ashley1888/ME-507-Term-Project/docs/gripper.png

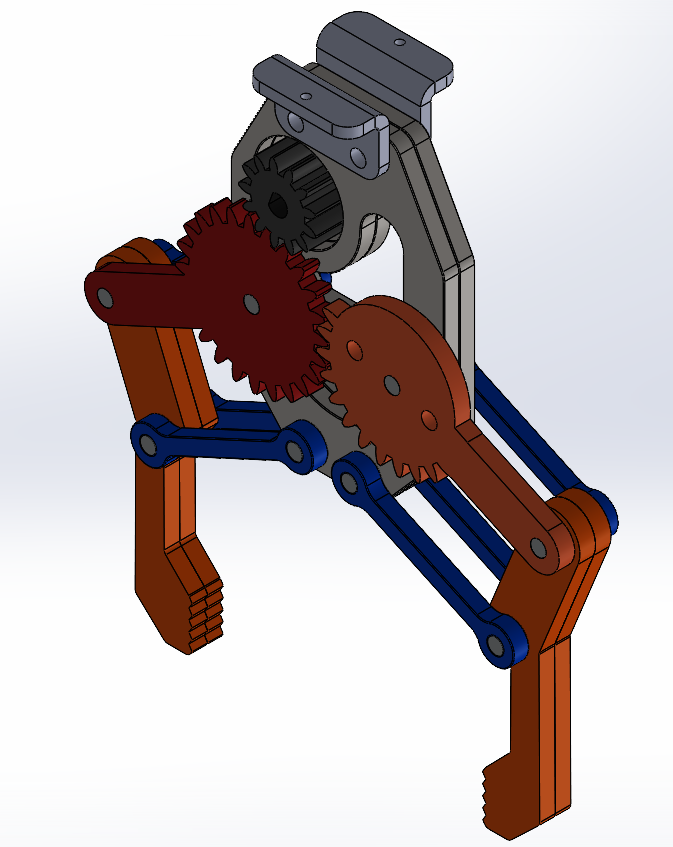
docs/gripper.png
