ashley1888/ME-507-Term-Project/docs/shaft_support_to_linear_bearing.png

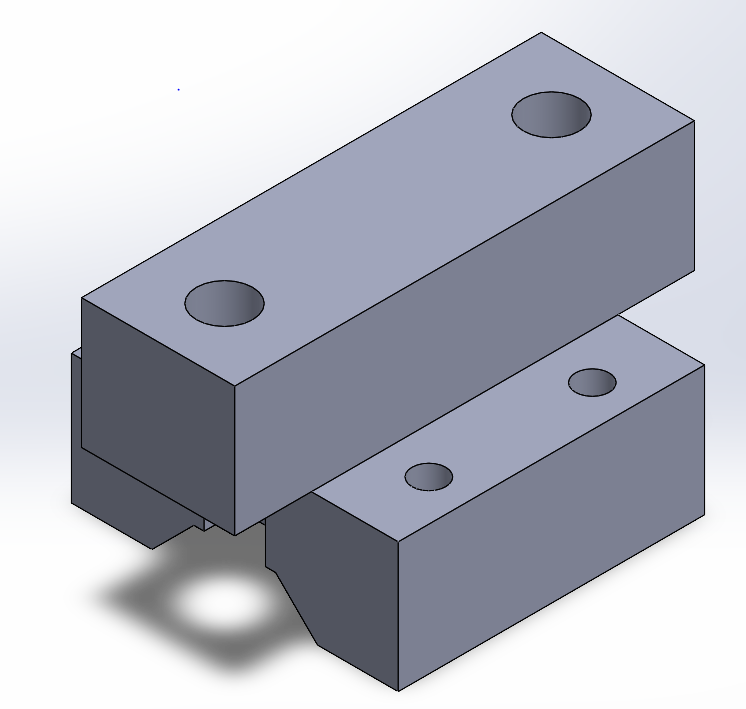
docs/shaft_support_to_linear_bearing.png
