ashley1888/ME-507-Term-Project/docs/x_motor_support.png

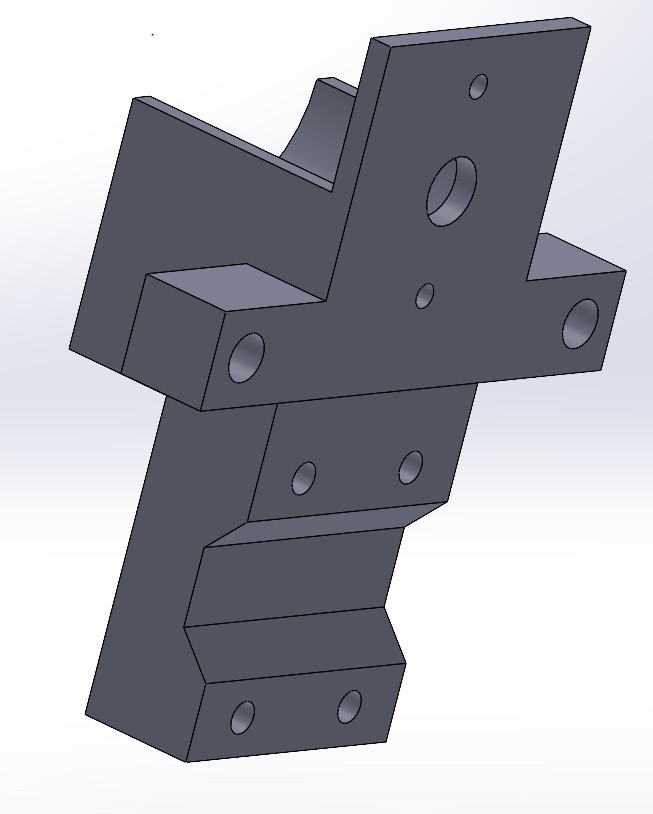
docs/x_motor_support.png
