ashley1888/ME-507-Term-Project/docs/z_motor_support.png

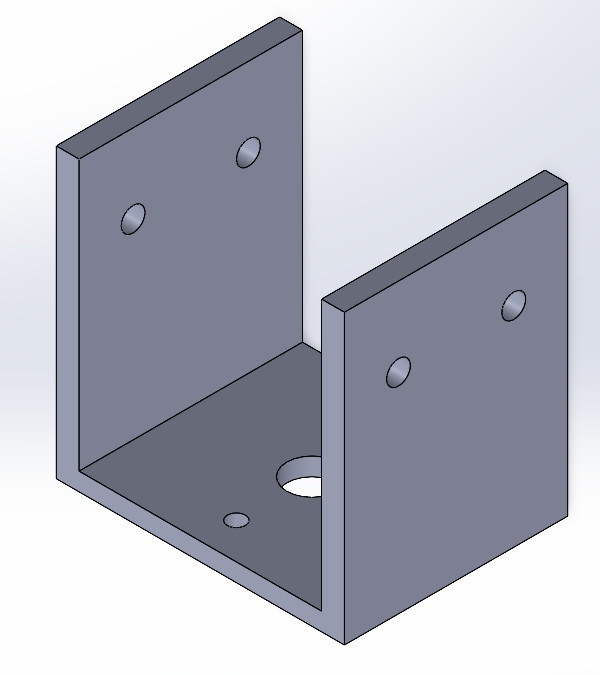
docs/z_motor_support.png
