ashley1888/ME-507-Term-Project/CAD/3D Printed Parts/Belt Clamp.SLDPRT

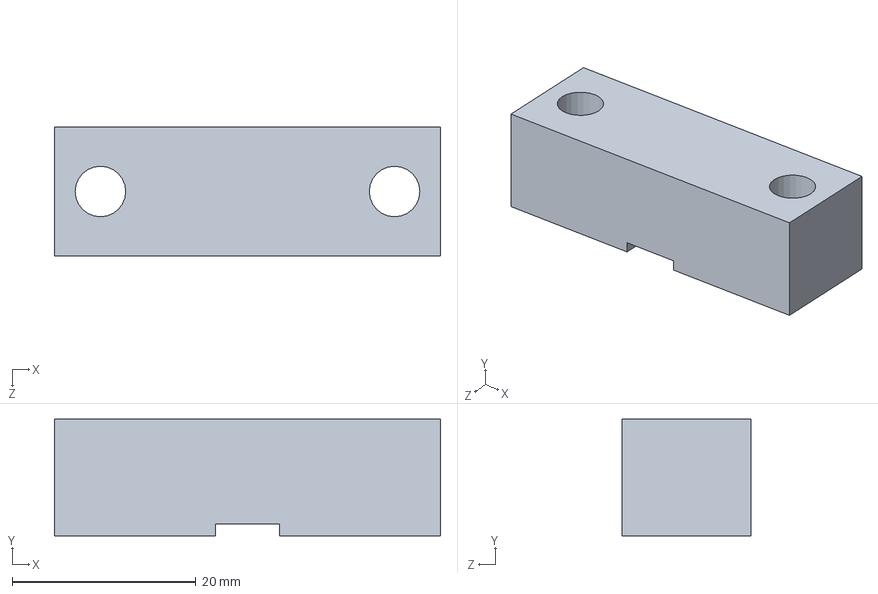
[picture p25: CAD file, 2021-12-07]
CAD/3D Printed Parts/Belt Clamp.SLDPRT
42.0 x 12.7 x 14.0 mm
