ashley1888/ME-507-Term-Project/CAD/Gripper/Part6-6.SLDPRT

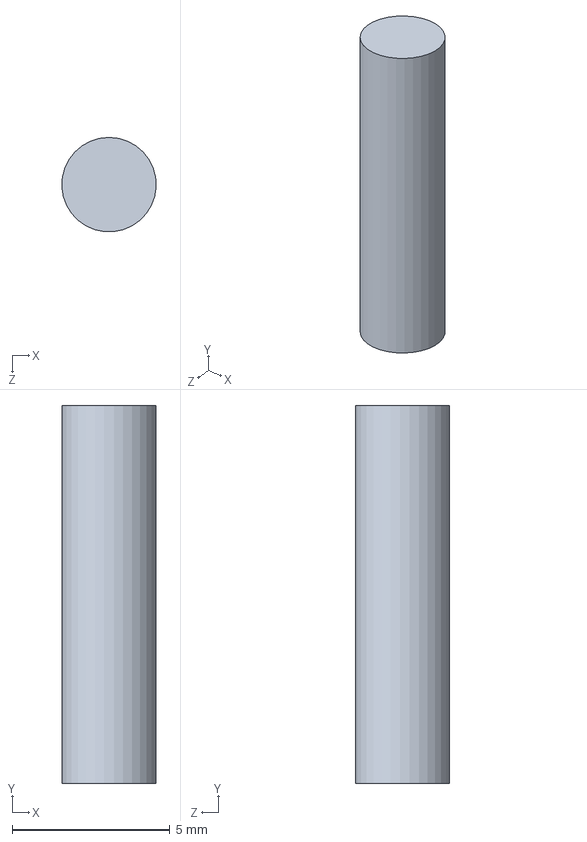
[picture p26: CAD file, 2021-12-07]
CAD/Gripper/Part6-6.SLDPRT
3.00 x 12.0 x 2.99 mm
