ashley1888/ME-507-Term-Project/CAD/Shaft Coupling.SLDPRT

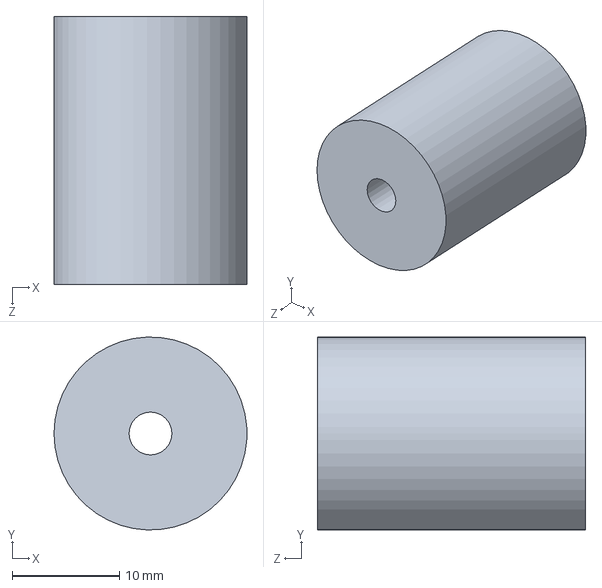
[picture p27: CAD file, 2021-12-07]
CAD/Shaft Coupling.SLDPRT
18.0 x 18.0 x 25.0 mm
