ashley1888/ME-507-Term-Project/CAD/3D Printed Parts/.stl Files/Part3-3 (x2).STL

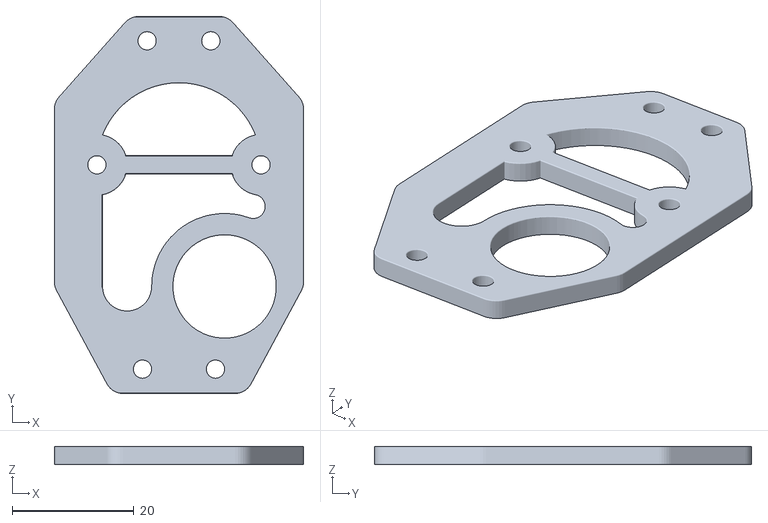
[picture p28: CAD file, 2021-12-08]
CAD/3D Printed Parts/.stl Files/Part3-3 (x2).STL
41.0 x 62.0 x 3.00
