ashley1888/ME-507-Term-Project/CAD/3D Printed Parts/Shaft Support to Linear Bearing.SLDPRT

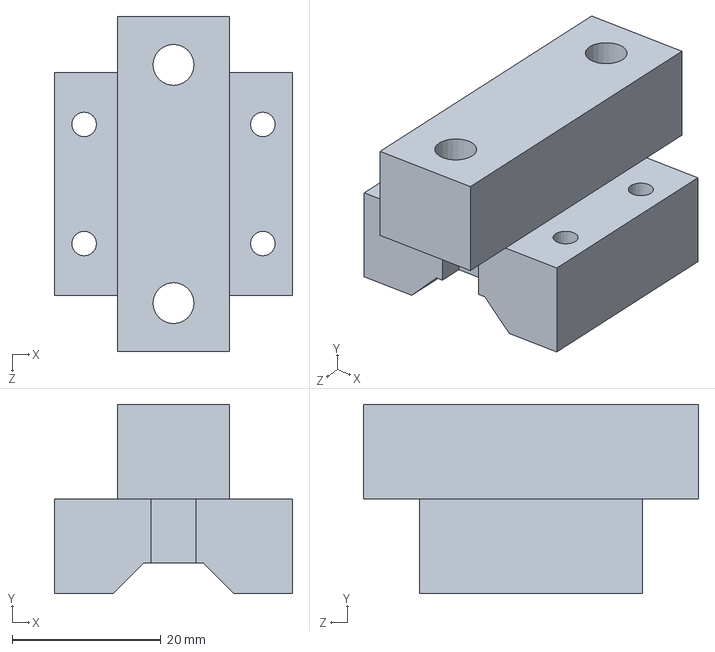
[picture p29: CAD file, 2021-12-07]
CAD/3D Printed Parts/Shaft Support to Linear Bearing.SLDPRT
32.0 x 25.4 x 45.0 mm
