ashley1888/ME-507-Term-Project/CAD/Motor.SLDPRT

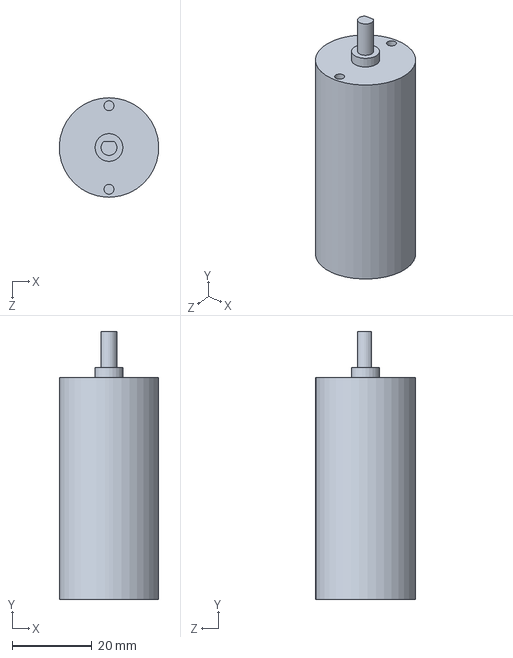
[picture p30: CAD file, 2021-12-07]
CAD/Motor.SLDPRT
25.0 x 67.3 x 25.0 mm
