ashley1888/ME-507-Term-Project/CAD/3D Printed Parts/.stl Files/Belt Holder (x2).STL

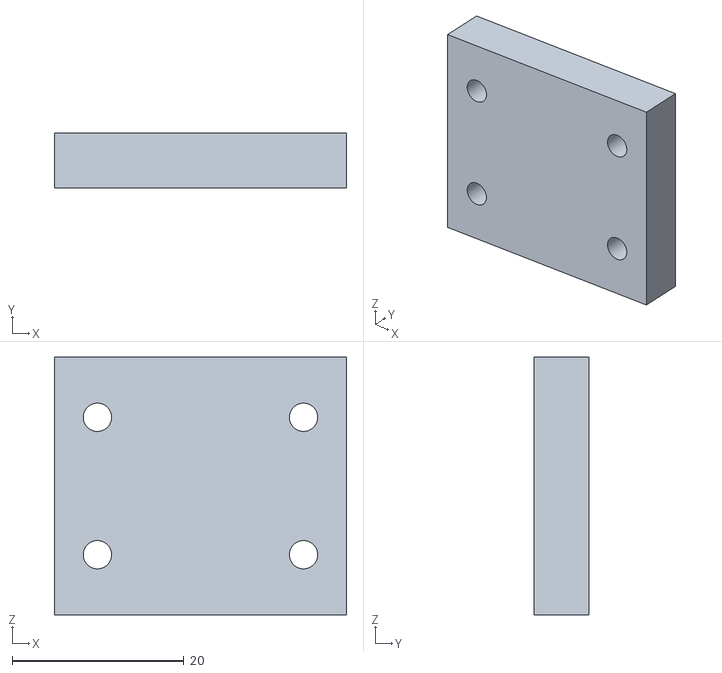
[picture p31: CAD file, 2021-12-08]
CAD/3D Printed Parts/.stl Files/Belt Holder (x2).STL
34.0 x 6.35 x 30.0
