ashley1888/ME-507-Term-Project/CAD/3D Printed Parts/Linear Rod Support Belt Holder.SLDPRT

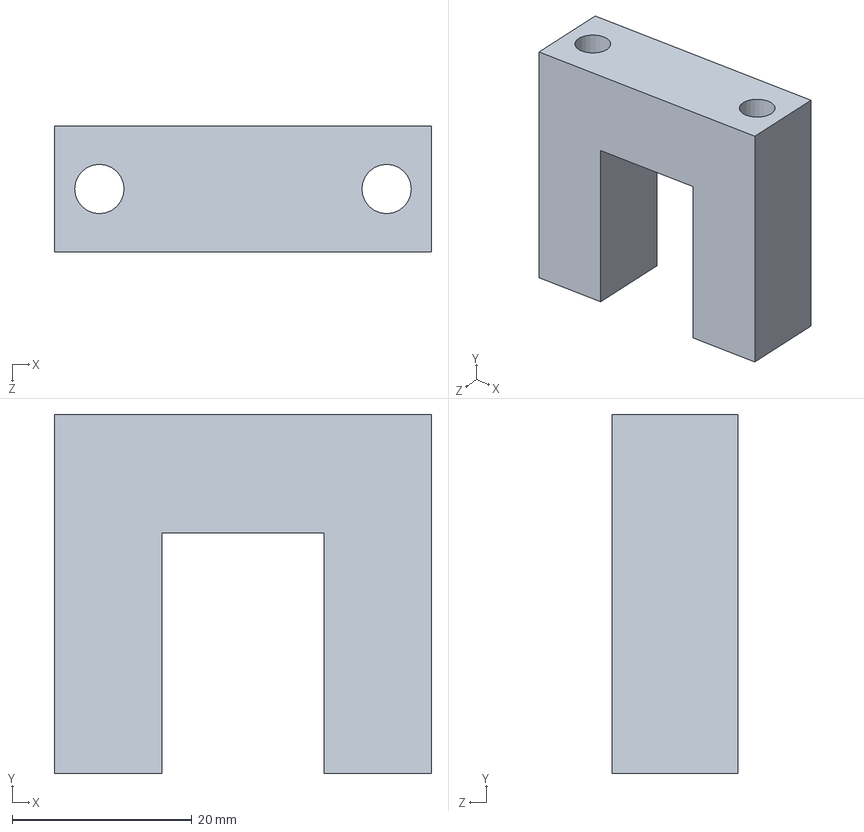
[picture p32: CAD file, 2021-12-07]
CAD/3D Printed Parts/Linear Rod Support Belt Holder.SLDPRT
42.0 x 40.0 x 14.0 mm
