ashley1888/ME-507-Term-Project/CAD/Gripper/Part7-7.SLDPRT

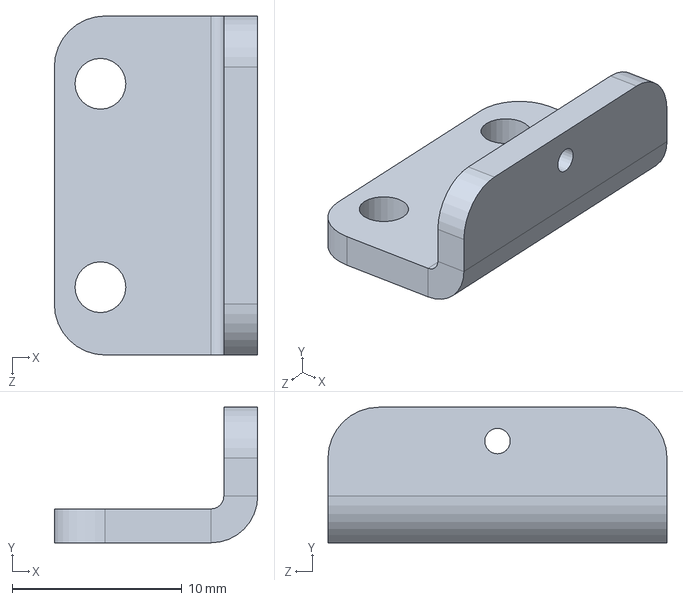
[picture p33: CAD file, 2021-12-07]
CAD/Gripper/Part7-7.SLDPRT
12.0 x 8.00 x 20.0 mm
