ashley1888/ME-507-Term-Project/CAD/Linear Ball Bearing.SLDPRT

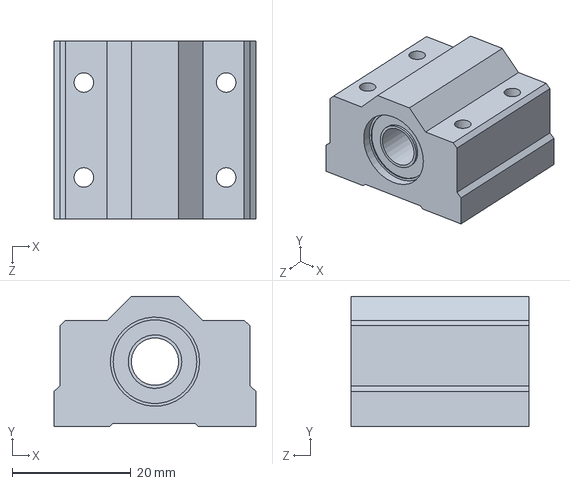
[picture p34: CAD file, 2021-12-07]
CAD/Linear Ball Bearing.SLDPRT
34.1 x 22.0 x 30.0 mm
