ashley1888/ME-507-Term-Project/CAD/3D Printed Parts/.stl Files/part4-4 (x1).STL

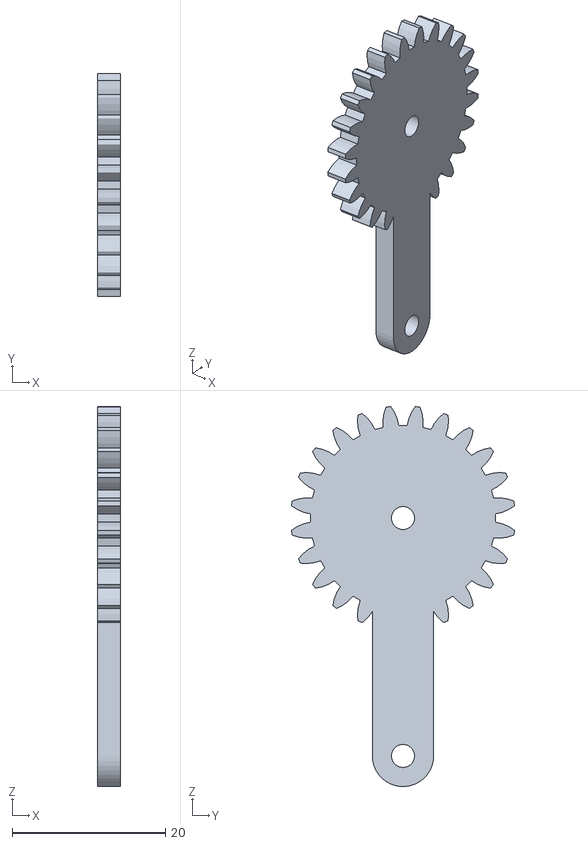
[picture p35: CAD file, 2021-12-08]
CAD/3D Printed Parts/.stl Files/part4-4 (x1).STL
3.00 x 29.1 x 49.5
