ashley1888/ME-507-Term-Project/CAD/Linear Rod.SLDPRT

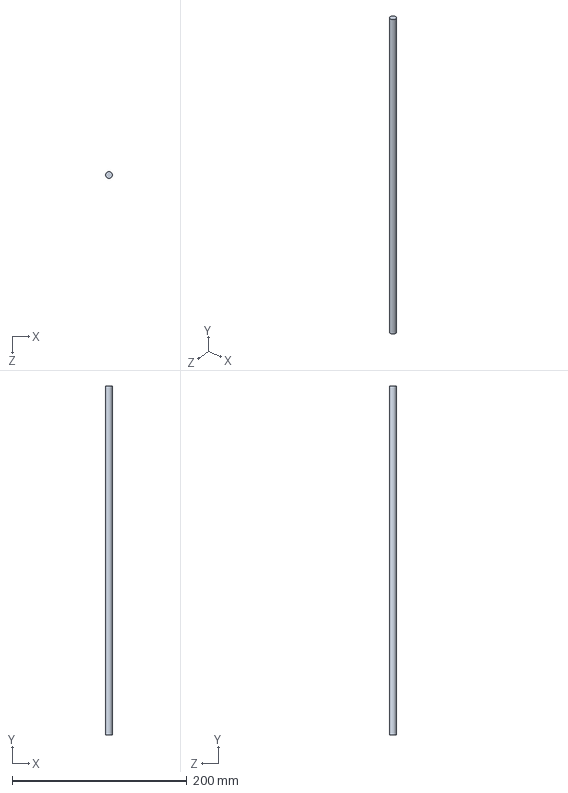
[picture p36: CAD file, 2021-12-07]
CAD/Linear Rod.SLDPRT
8.00 x 400.0 x 8.00 mm
