ashley1888/ME-507-Term-Project/CAD/Linear Rod Support.SLDPRT

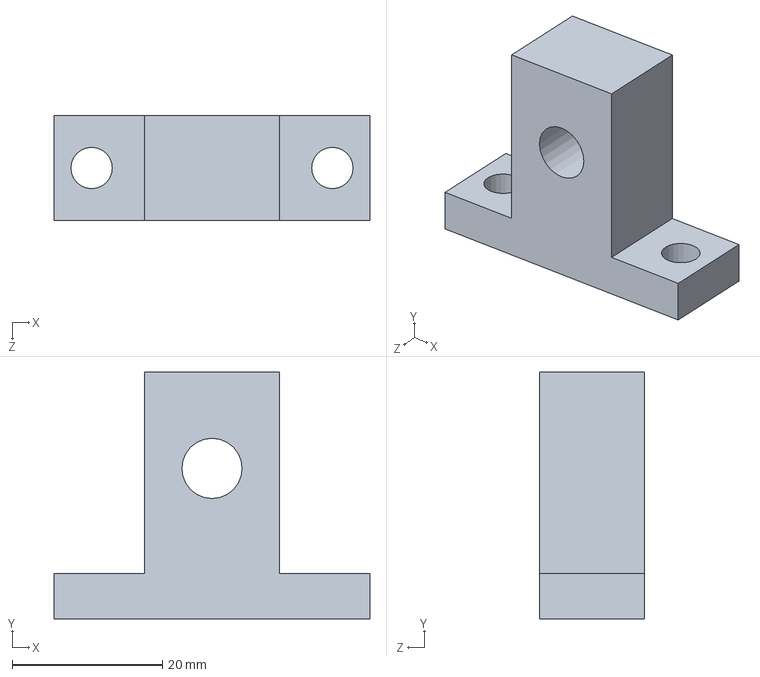
[picture p37: CAD file, 2021-12-07]
CAD/Linear Rod Support.SLDPRT
42.0 x 32.8 x 14.0 mm
