ashley1888/ME-507-Term-Project/CAD/Gear Pulley.SLDPRT

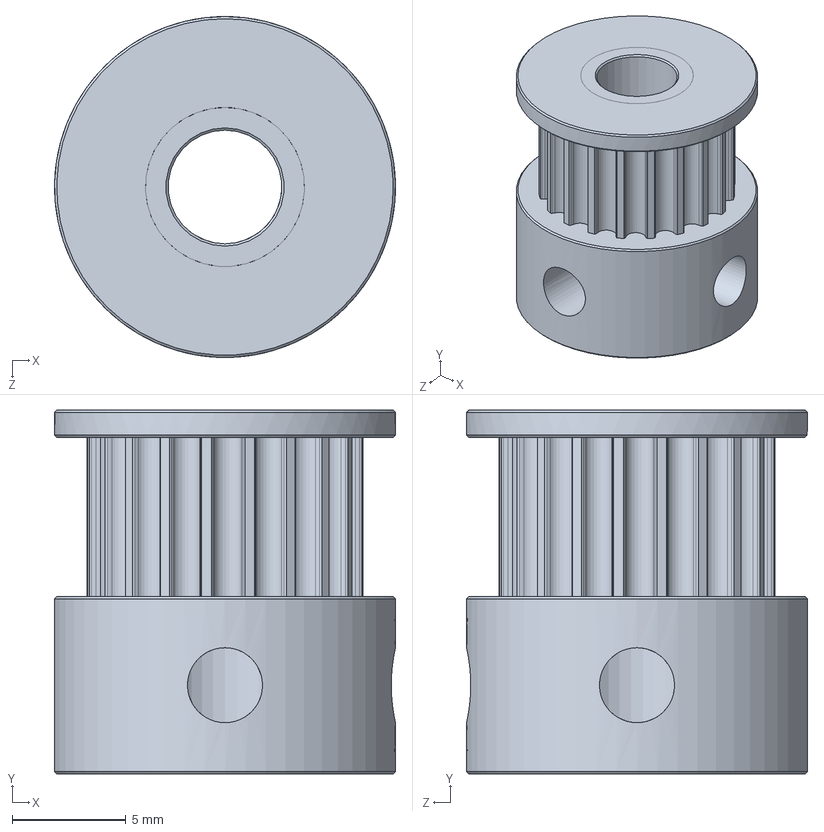
[picture p38: CAD file, 2021-12-07]
CAD/Gear Pulley.SLDPRT
15.0 x 16.0 x 15.0 mm
