ashley1888/ME-507-Term-Project/ME 507 Clawmachine/src/Gripper_Motor_Task.h

/** @file Gripper_Motor_Task.h
 *  This file contains a header for the gripper-motor task.
 * 
 *  @author Michael Yiu and Ashley Humpal
 *  @date   2021-Dec-01
 */

#ifndef _GRIPPER_MOTOR_TASK_H_
#define _GRIPPER_MOTOR_TASK_H_

void task_gripper_motor (void* p_params);

#endif // _GRIPPER_MOTOR_TASK_H_
