ashley1888/ME-507-Term-Project/ME 507 Clawmachine/src/X_Motor_Task.h

/** @file X_Motor_Task.h
 *  This file contains a header for the x-motor task.
 * 
 *  @author Michael Yiu and Ashley Humpal
 *  @date   2021-Dec-01
 */

#ifndef _MOTORX_TASK_H_
#define _MOTORX_TASK_H_

void task_x_motor (void* p_params);

#endif // _MOTORX_TASK_H_
