ashley1888/ME-507-Term-Project/ME 507 Clawmachine/src/Y_Motor_Task.h

/** @file Y_Motor_Task.h
 *  This file contains a header for the y-motor task.
 * 
 *  @author Michael Yiu and Ashley Humpal
 *  @date   2021-Dec-01
 */

#ifndef _MOTORY_TASK_H_
#define _MOTORY_TASK_H_

void task_y_motor (void* p_params);

#endif // _MOTORY_TASK_H_
