ashley1888/ME-507-Term-Project/ME 507 Clawmachine/src/Z_Motor_Task.h

/** @file Z_Motor_Task.h
 *  This file contains a header for the z-motor task.
 * 
 *  @author Michael Yiu and Ashley Humpal
 *  @date   2021-Dec-01
 */

#ifndef _MOTORZ_TASK_H_
#define _MOTORZ_TASK_H_

void task_z_motor (void* p_params);

#endif // _MOTORZ_TASK_H_
